Jana-Marie/transpOtterNG/Image/docs/base.jpg

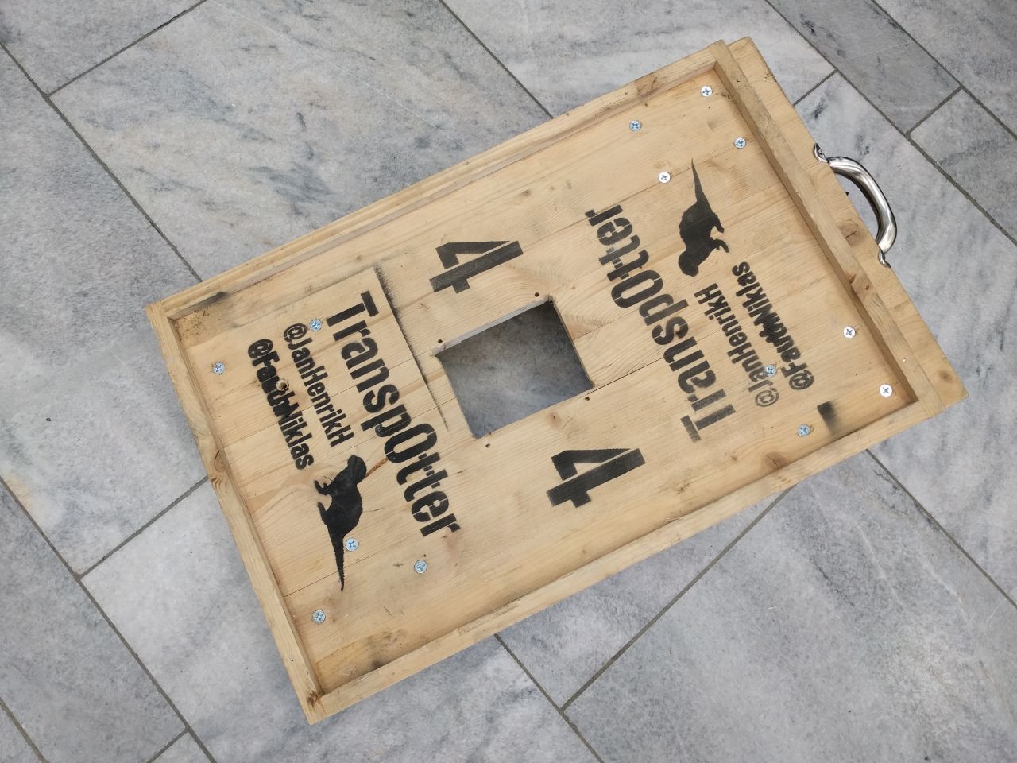
Image/docs/base.jpg
