Jana-Marie/transpOtterNG/Image/docs/connect_programming_jack.jpg

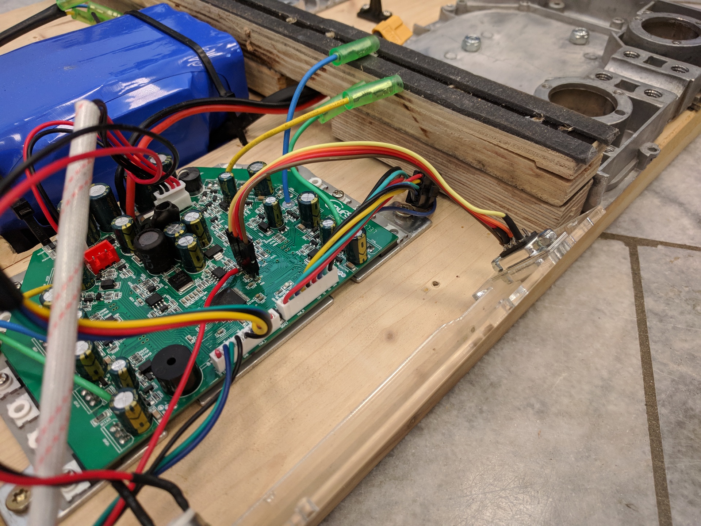
Image/docs/connect_programming_jack.jpg
