Jana-Marie/transpOtterNG/Image/docs/external_programming_jack.jpg

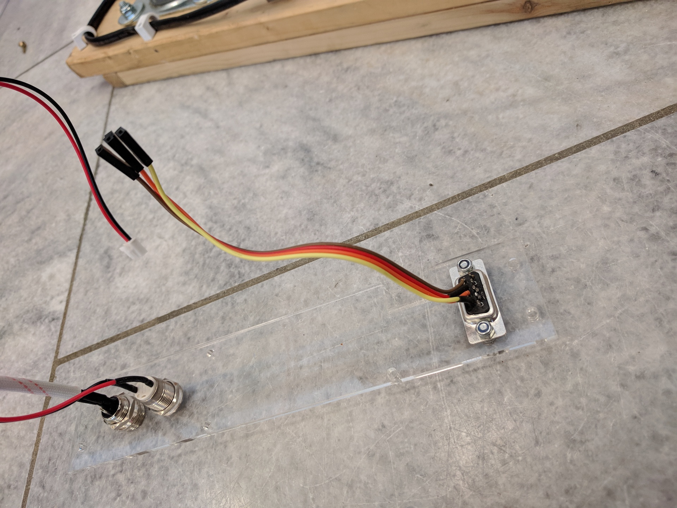
Image/docs/external_programming_jack.jpg
