Jana-Marie/transpOtterNG/Image/docs/gametrak_cable_connection.jpg

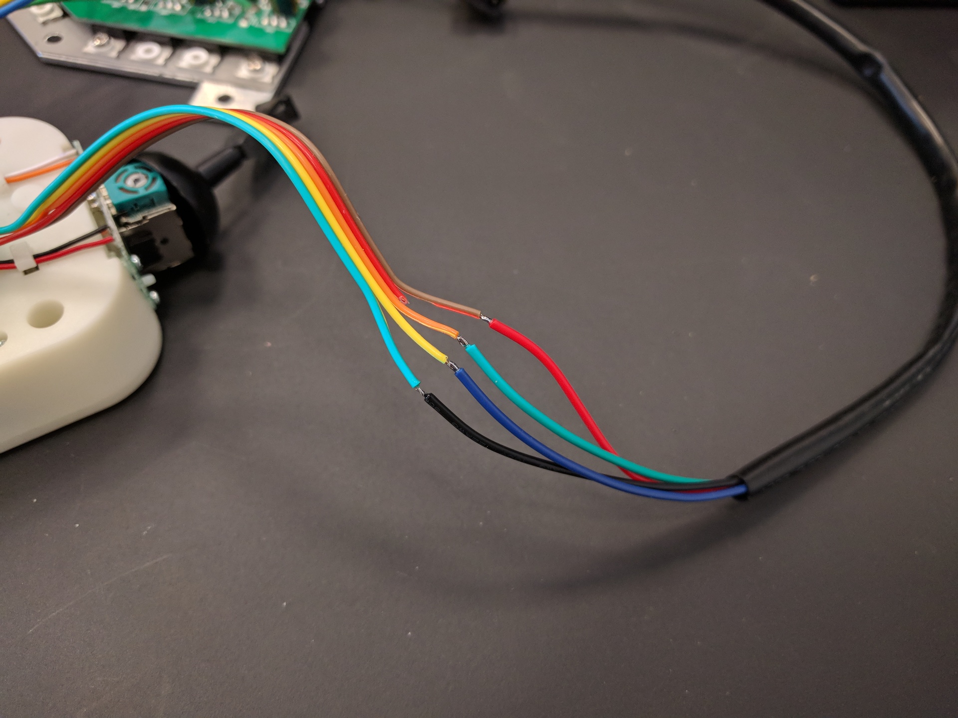
Image/docs/gametrak_cable_connection.jpg
