Jana-Marie/transpOtterNG/Image/docs/gametrak_opened.jpg

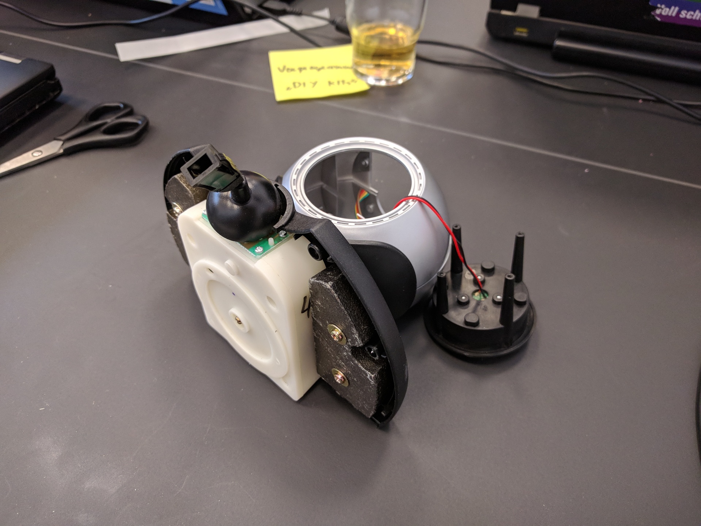
Image/docs/gametrak_opened.jpg
