Jana-Marie/transpOtterNG/Image/docs/gametrak_removed.jpg

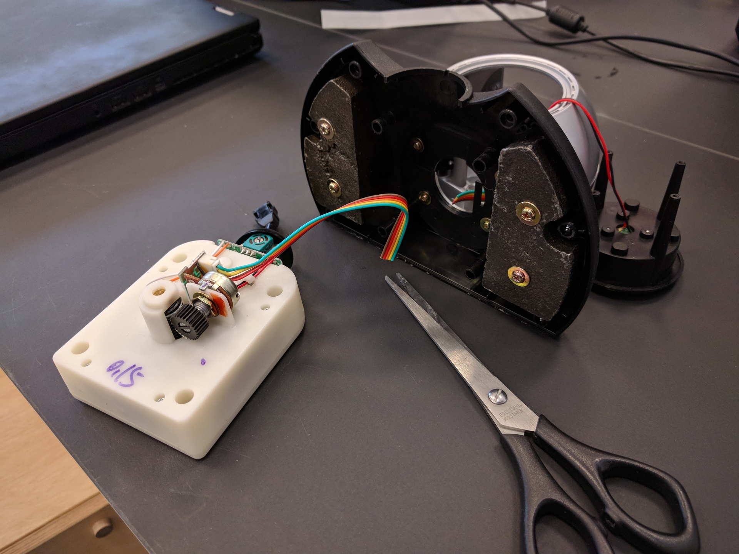
Image/docs/gametrak_removed.jpg
