Jana-Marie/transpOtterNG/Image/docs/gametrak_wire.jpg

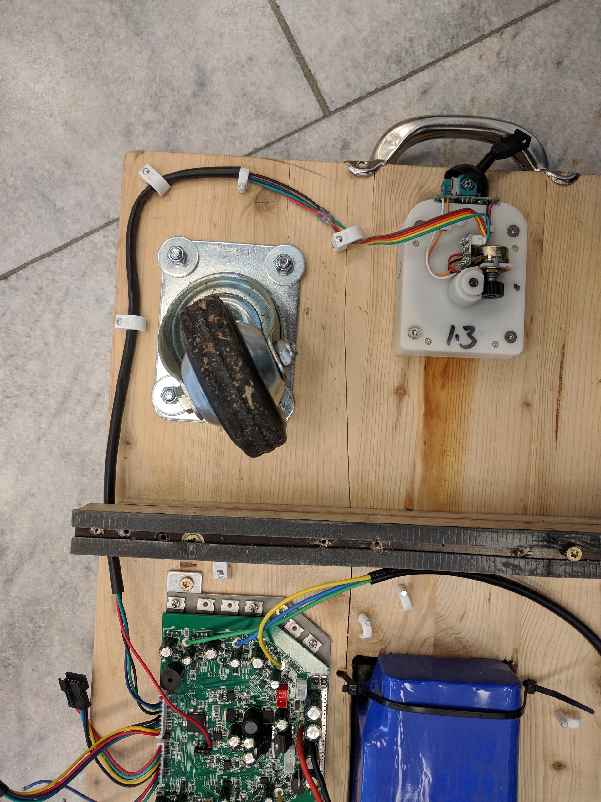
Image/docs/gametrak_wire.jpg
