Jana-Marie/transpOtterNG/Image/docs/hot_glue.jpg

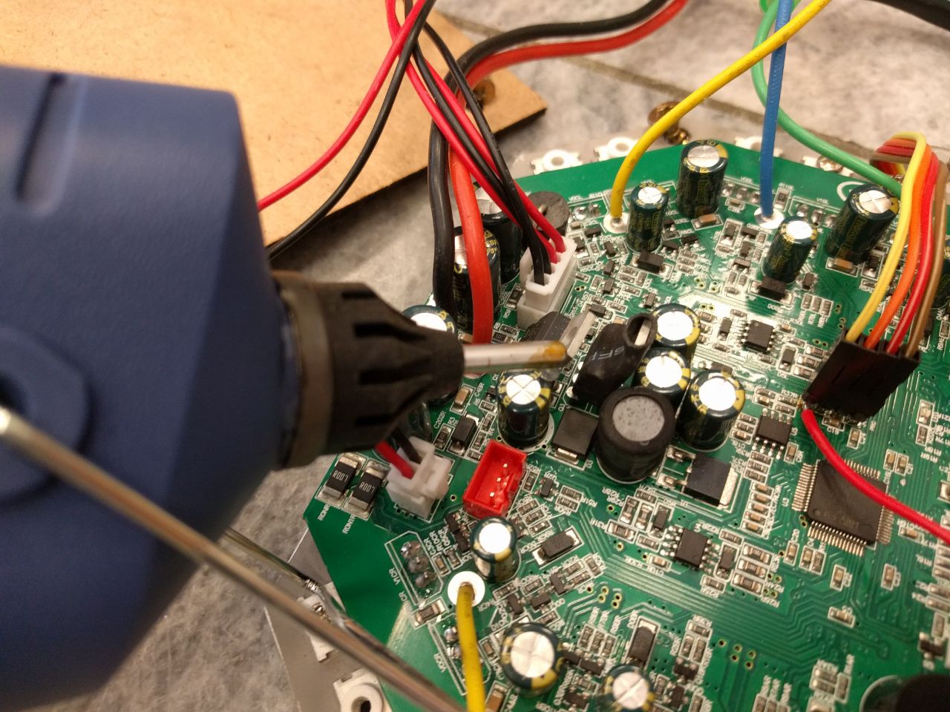
Image/docs/hot_glue.jpg
