Jana-Marie/transpOtterNG/Image/docs/motor_bracket_hacksaw.jpg

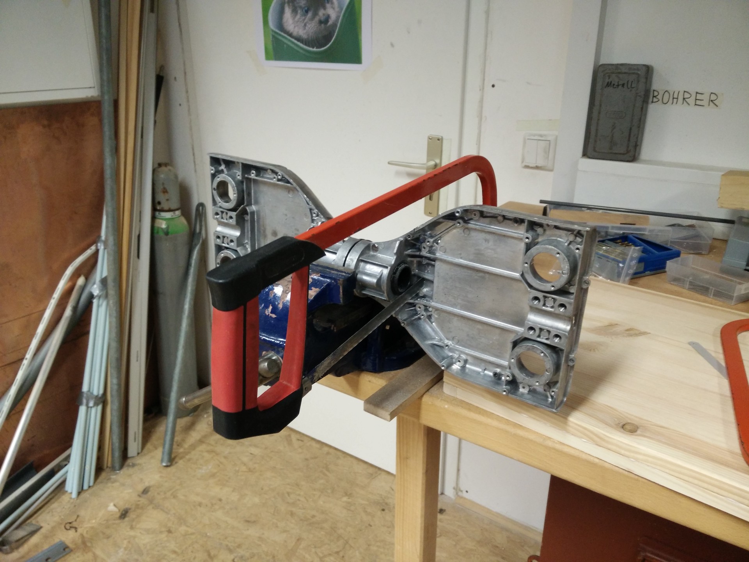
Image/docs/motor_bracket_hacksaw.jpg
