Jana-Marie/transpOtterNG/Image/docs/motor_bracket_mount.jpg

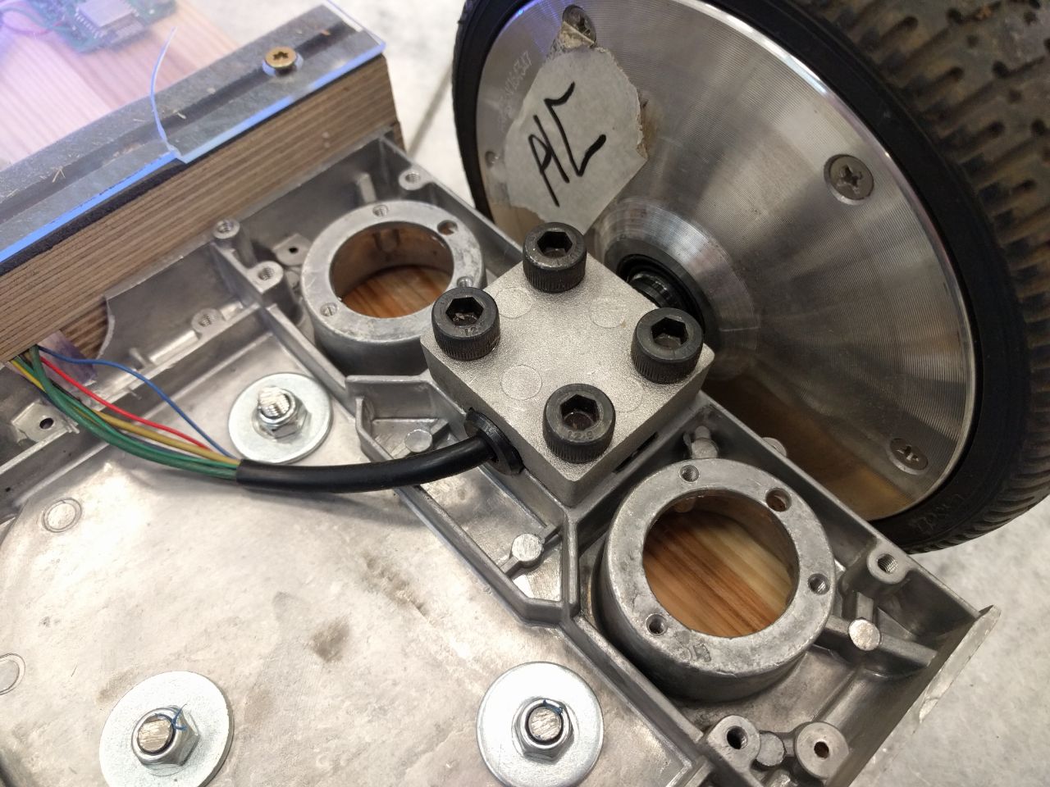
Image/docs/motor_bracket_mount.jpg
