Jana-Marie/transpOtterNG/Image/docs/pinheader_detail_wo.jpg

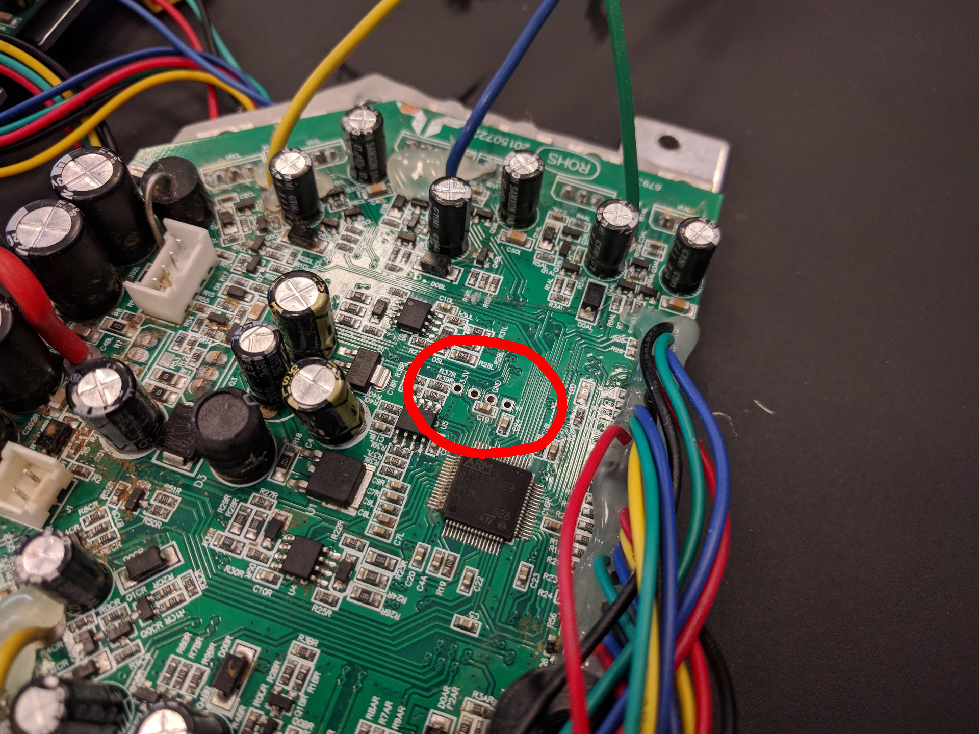
Image/docs/pinheader_detail_wo.jpg
