Jana-Marie/transpOtterNG/Image/docs/st-link_connection.jpg

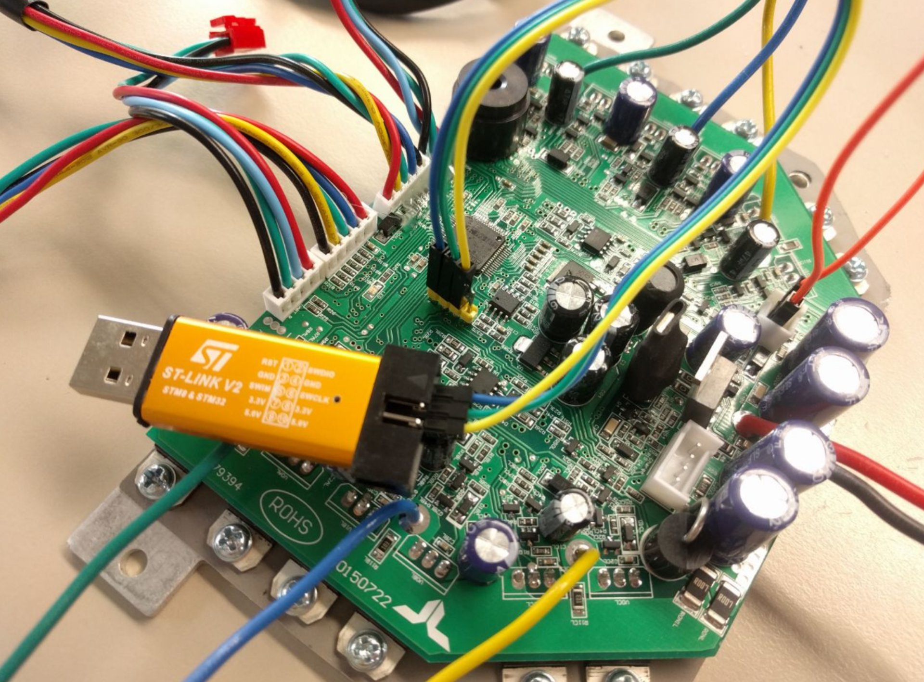
Image/docs/st-link_connection.jpg
