Jana-Marie/transpOtterNG/Image/docs/tin_cable_tips.jpg

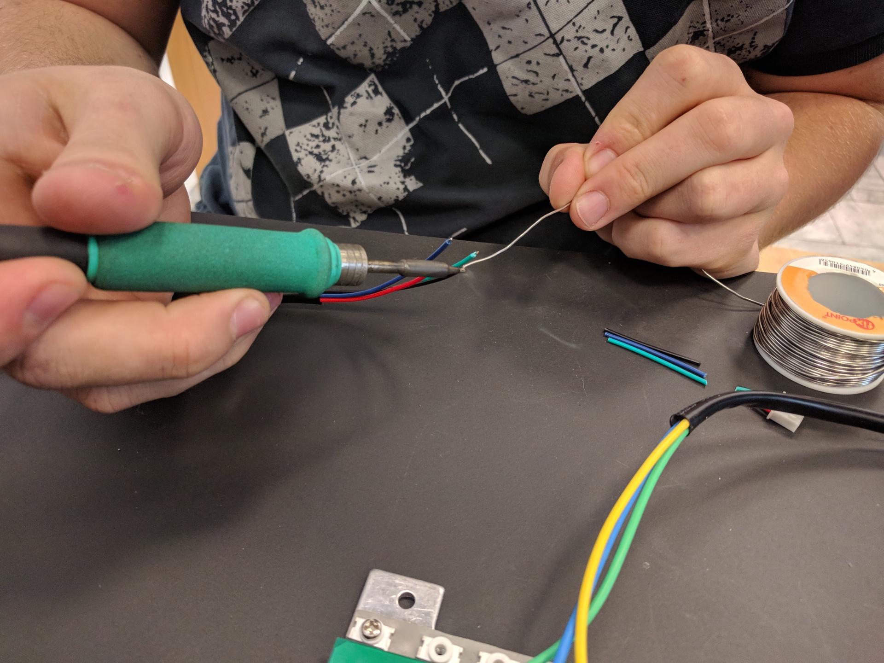
Image/docs/tin_cable_tips.jpg
