Jana-Marie/transpOtterNG/Image/docs/transpotter_top.jpg

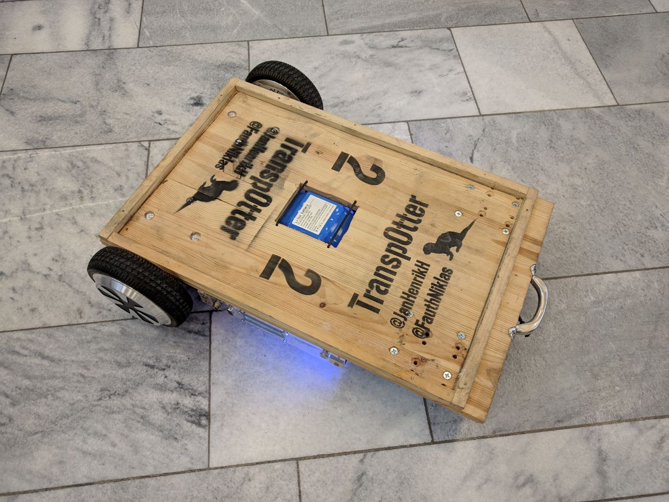
Image/docs/transpotter_top.jpg
