Jana-Marie/transpOtterNG/Image/docs/wheel.jpg

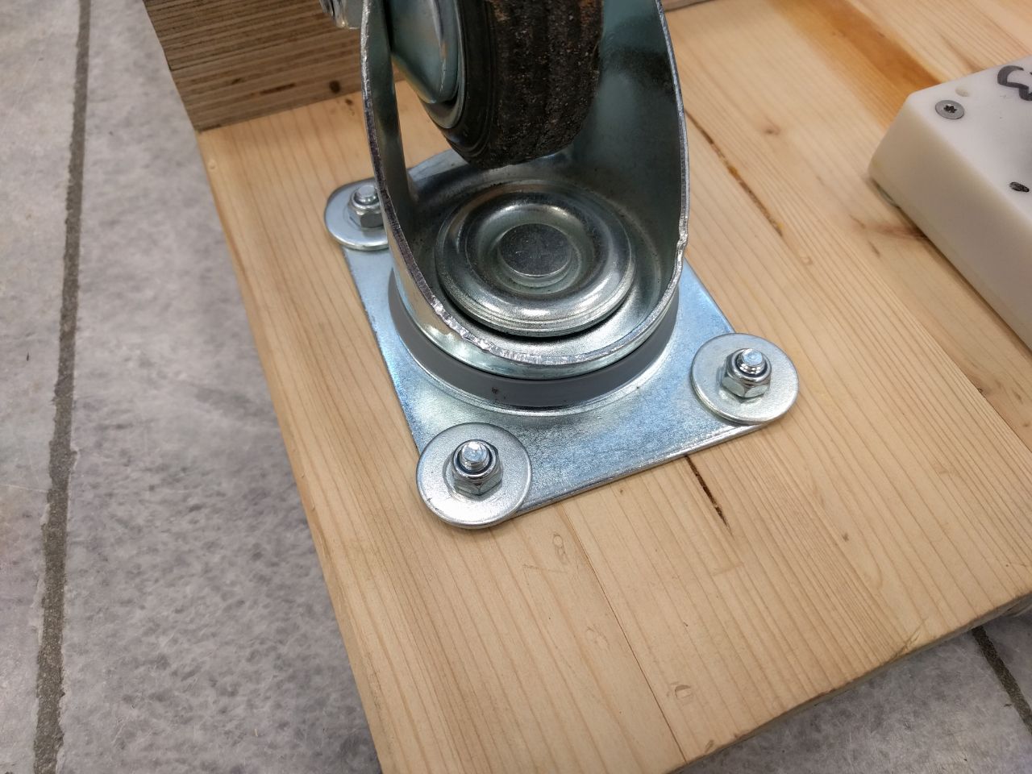
Image/docs/wheel.jpg
