Jana-Marie/transpOtterNG/Image/docs/which_cable_to_cut.jpg

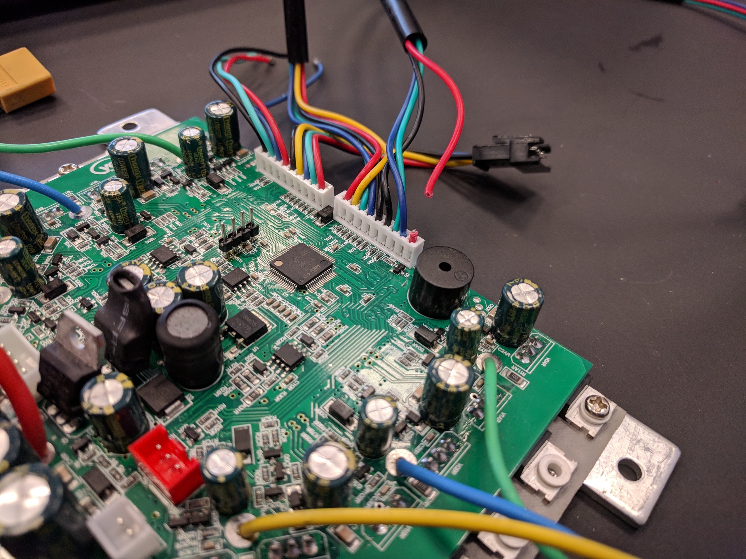
Image/docs/which_cable_to_cut.jpg
