Jana-Marie/transpOtterNG/Image/docs/xt60_safety.jpg

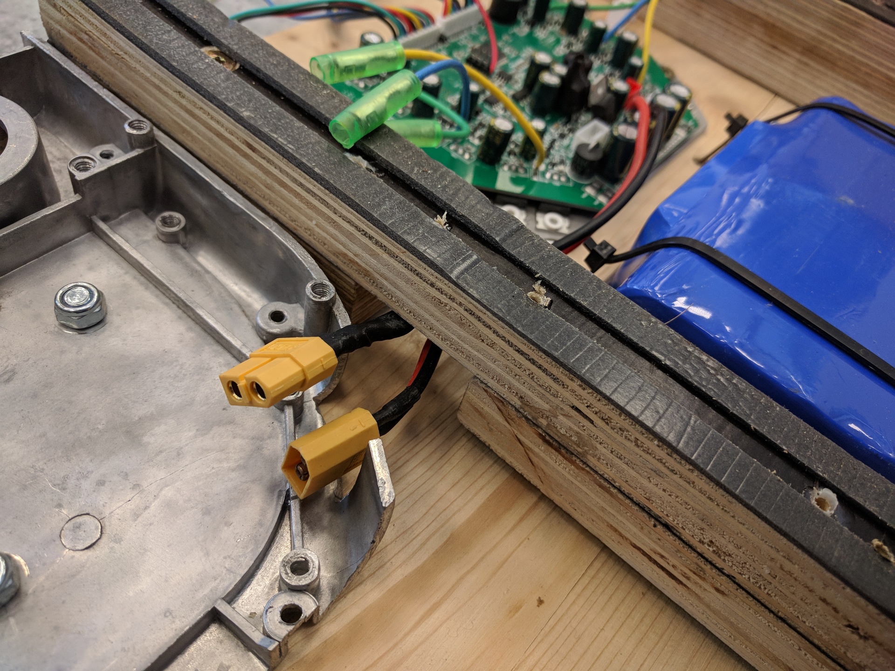
Image/docs/xt60_safety.jpg
