Jana-Marie/transpOtterNG/kicad/Images/PCB_Back.png

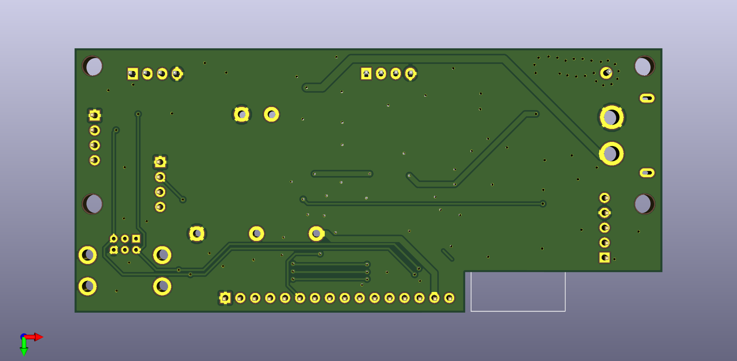
kicad/Images/PCB_Back.png
