Jana-Marie/transpOtterNG/kicad/Images/PCB_Front.png

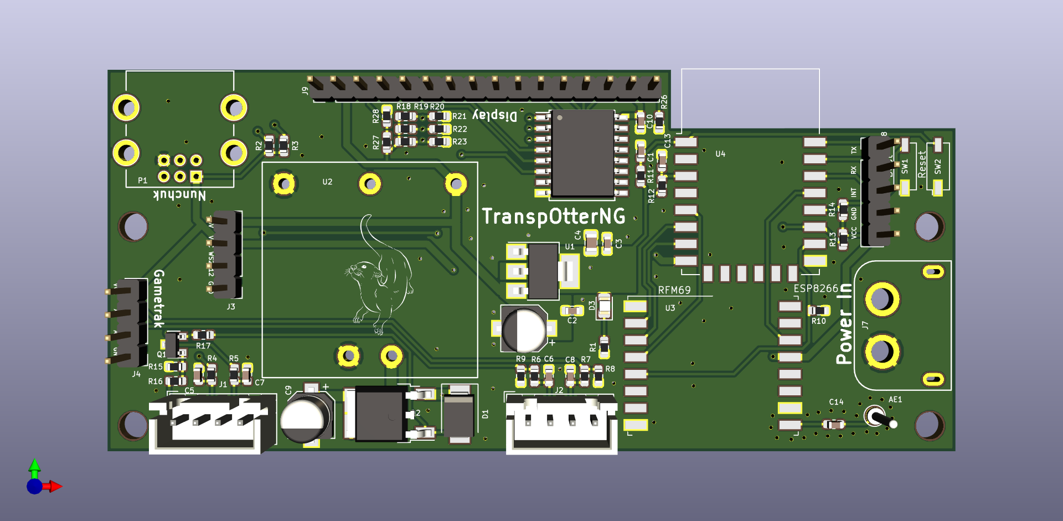
kicad/Images/PCB_Front.png
