Jana-Marie/transpOtterNG/Image/docs/howto_mount_alu.jpg

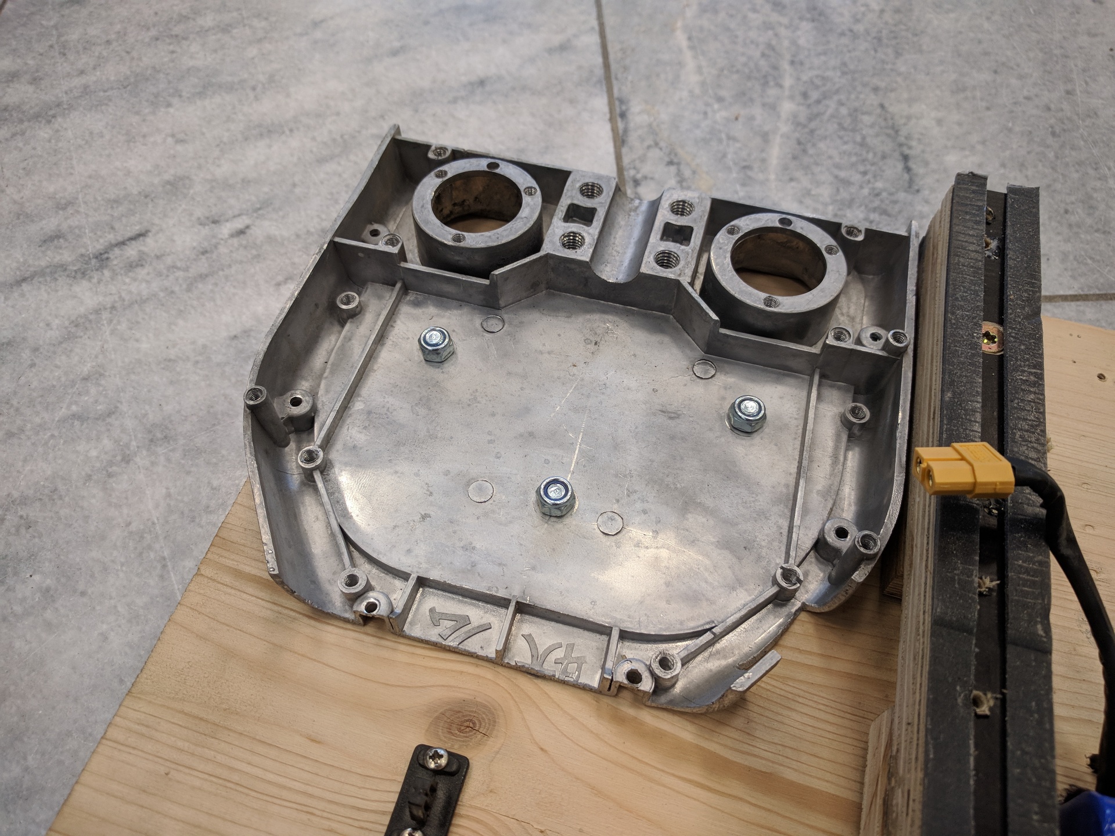
Image/docs/howto_mount_alu.jpg
