Jana-Marie/transpOtterNG/Image/docs/howto_mount_battery.jpg

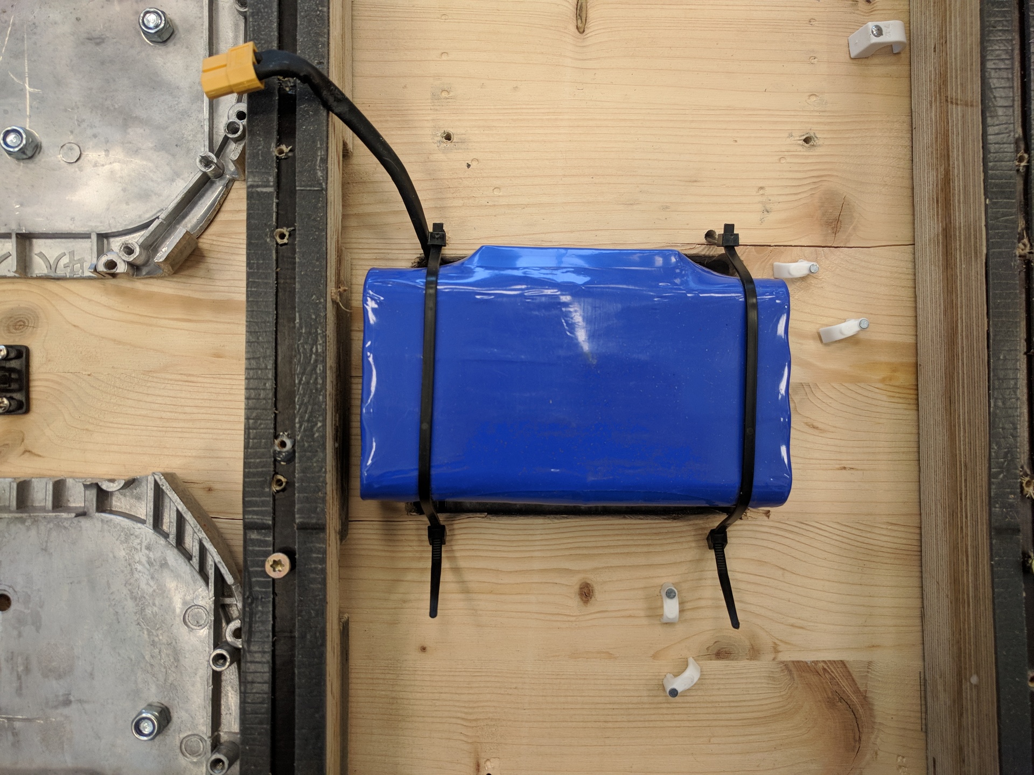
Image/docs/howto_mount_battery.jpg
