Jana-Marie/transpOtterNG/Image/docs/howto_mount_gametrak.jpg

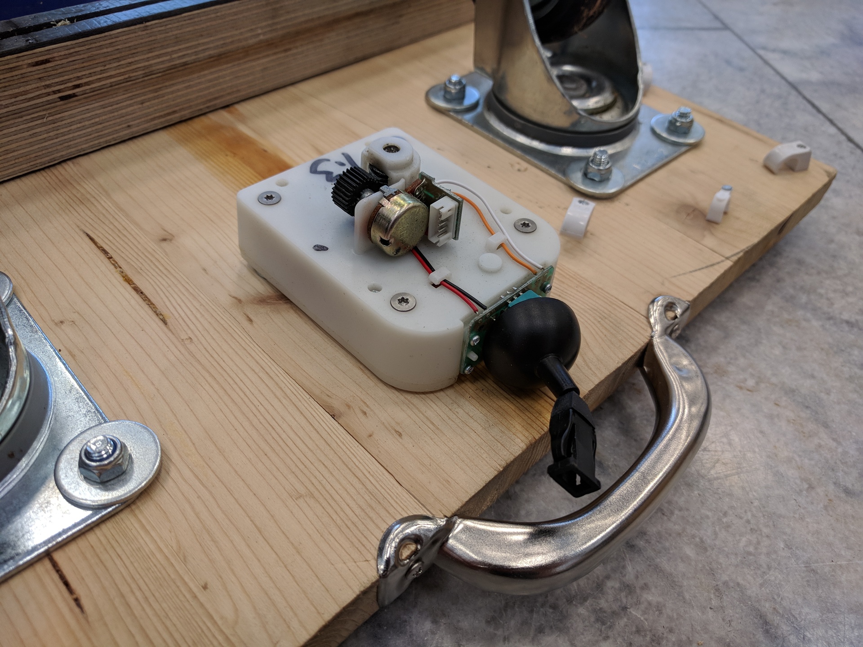
Image/docs/howto_mount_gametrak.jpg
