Jana-Marie/transpOtterNG/Image/docs/howto_mount_gametral_washer.jpg

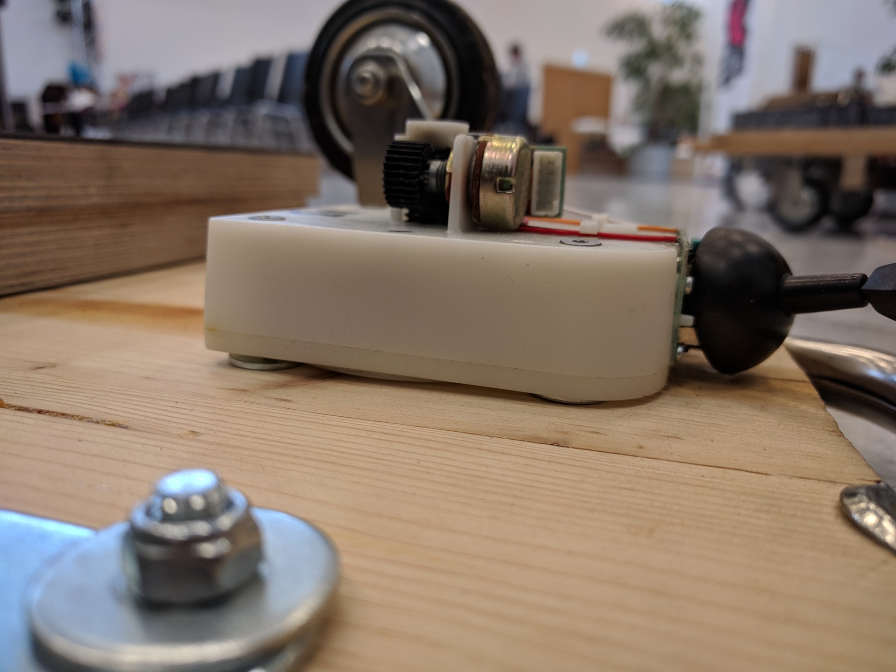
Image/docs/howto_mount_gametral_washer.jpg
