Jana-Marie/transpOtterNG/Image/docs/howto_mount_mainboard.jpg

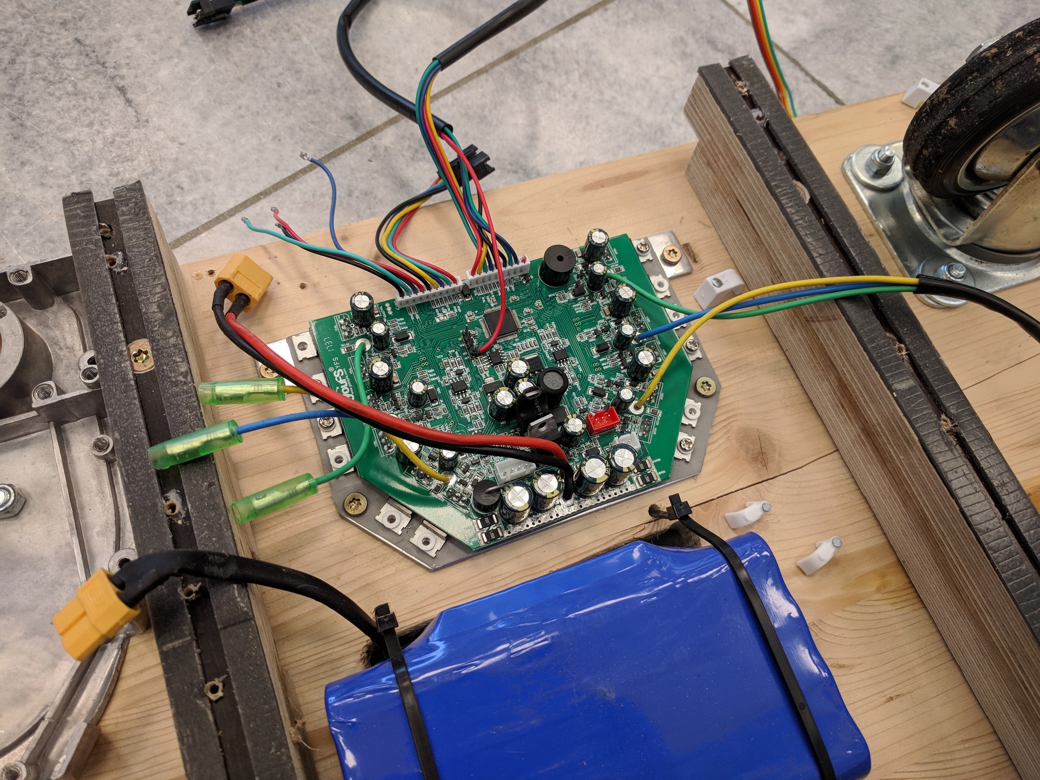
Image/docs/howto_mount_mainboard.jpg
