Jana-Marie/transpOtterNG/Image/docs/pinheader_detail_soldered.jpg

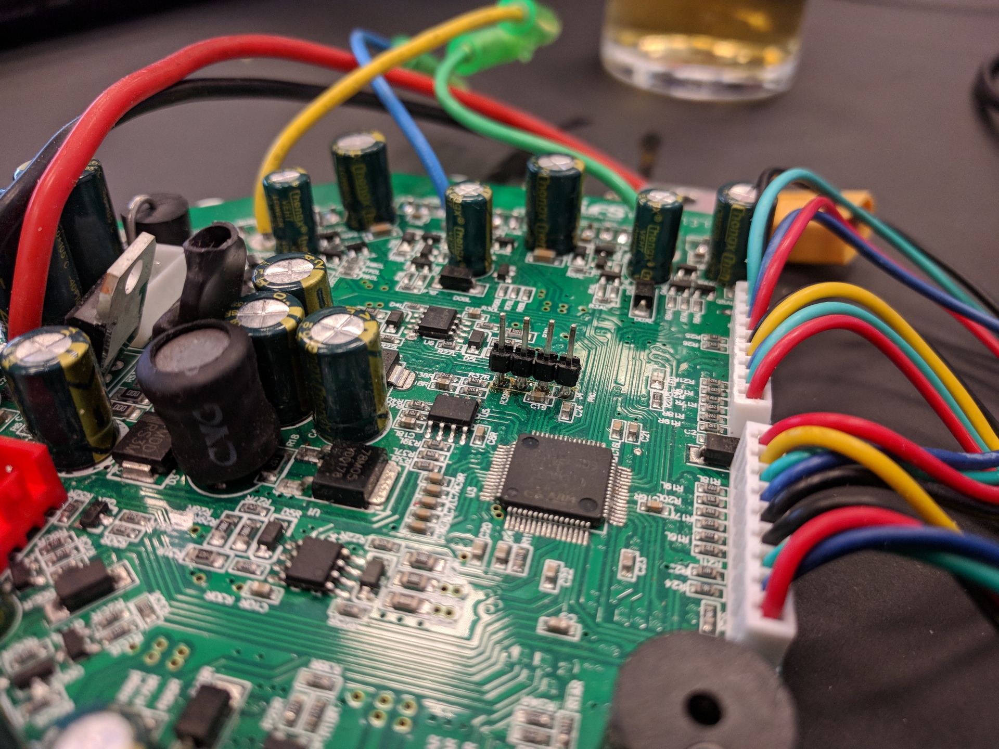
Image/docs/pinheader_detail_soldered.jpg
