Jana-Marie/transpOtterNG/Image/docs/pinheader_detail_unsoldered.jpg

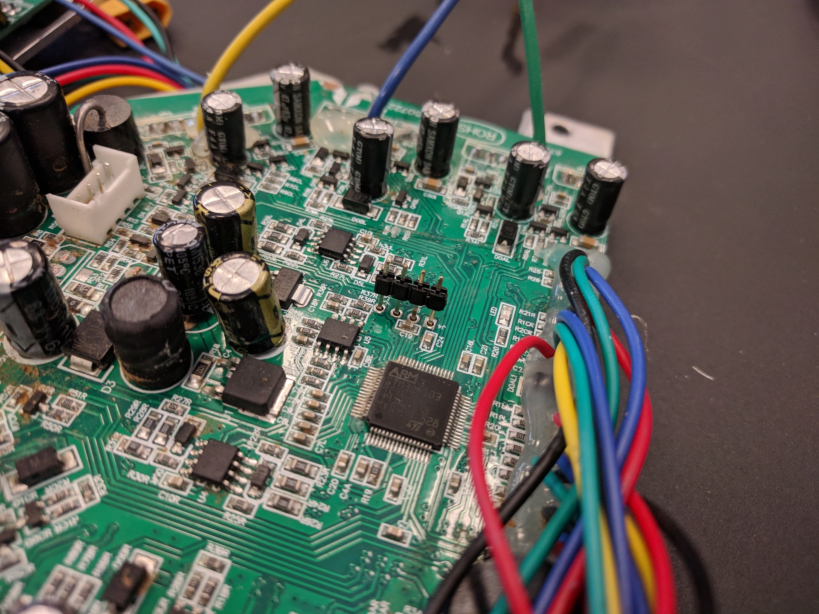
Image/docs/pinheader_detail_unsoldered.jpg
